OeMga-me/oemga-hardware/hardware/Photos/1769923947423.jpeg

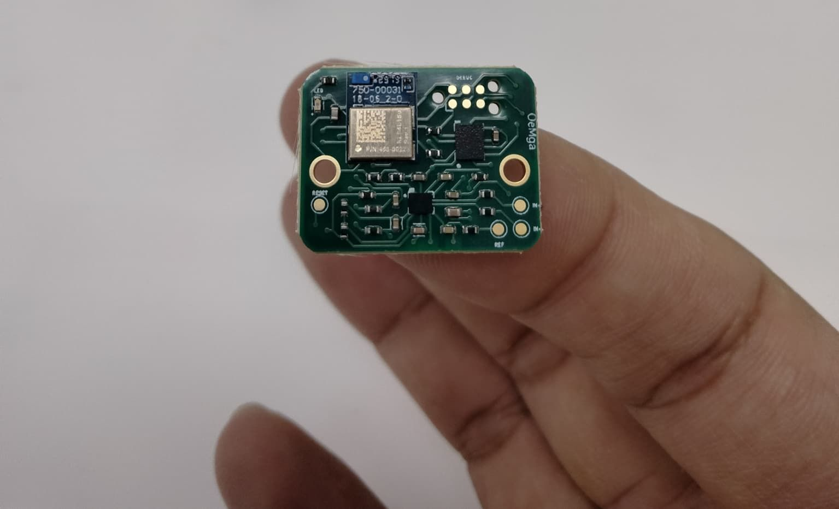
hardware/Photos/1769923947423.jpeg
